saybur/hootswitch/firmware/control.c

/*
 * Copyright (C) 2024-2026 saybur
 *
 * This Source Code Form is subject to the terms of the Mozilla Public
 * License, v. 2.0. If a copy of the MPL was not distributed with this
 * file, You can obtain one at https://mozilla.org/MPL/2.0/.
 */

#include <stdio.h>
#include <hardware/watchdog.h>

#include <tusb.h>

#include <FreeRTOS.h>
#include <stream_buffer.h>
#include <task.h>

#include "computer.h"
#include "config.h"
#include "control.h"
#include "debug.h"

#include "drivers/serial.h"

#ifdef HOOTSWITCH_WIRELESS
#include "btscan.h"
#endif

#define WATCHDOG_SCRATCH_REG   0

#define CONTROL_WDRST_DEBUG    0xA5A5A5A5
#define CONTROL_BUFFER_SIZE    64

#define CONTROL_CHAR_END       0xC0
#define CONTROL_CHAR_ESC       0xDB
#define CONTROL_CHAR_ESC_END   0xDC
#define CONTROL_CHAR_ESC_ESC   0xDD

static void control_reboot(bool debug)
{
	// set flag to pause restarting, if needed
	if (debug) {
		watchdog_hw->scratch[WATCHDOG_SCRATCH_REG] = CONTROL_WDRST_DEBUG;
	}

	// perform watchdog reset
	watchdog_enable(1, 1);
	while(1);
}

control_reset_type control_check_reset(void)
{
	// retrieve and clear any special flags
	uint32_t w = watchdog_hw->scratch[WATCHDOG_SCRATCH_REG];
	watchdog_hw->scratch[WATCHDOG_SCRATCH_REG] = 0;

	// if the watchdog was responsible for the reset,
	// check if it was a special condition we need to report
	if (watchdog_enable_caused_reboot()) {
		switch (w) {
			case CONTROL_WDRST_DEBUG:
				return RESET_TYPE_DEBUG;
		}
	}

	// fallback to normal
	return RESET_TYPE_NORMAL;
}

/*
 * ----------------------------------------------------------------------------
 *   SLIP Decoding
 * ----------------------------------------------------------------------------
 *
 * This is stateful, ensure it only gets called from the control task.
 */

static uint8_t control_buffer[CONTROL_BUFFER_SIZE];
static uint8_t control_buffer_length;

static void control_enqueue(unsigned char c)
{
	if (control_buffer_length < CONTROL_BUFFER_SIZE) {
		control_buffer[control_buffer_length++] = c;
	} else {
		dbg_err("control overflow!");
	}
}

static void control_commit(void)
{
	/*
	 * Don't consider no-op ends to be an error, serial interface may do this
	 * to reset the session.
	 */
	if (control_buffer_length < 1) return;

	if (control_buffer[0] >= CONTROL_CODE_SEGMENT) {
		switch (control_buffer[0]) {
			case CONTROL_BT_SCAN:
#ifdef HOOTSWITCH_WIRELESS
				bt_scan();
#endif
				break;
			case CONTROL_DBG_TRACE:
				dbg_trace_enable(!dbg_trace_is_enabled());
				break;
			case CONTROL_DBG_HEAP:
				dbg_stats(DEBUG_RUNTIME_HEAP);
				break;
			case CONTROL_DBG_LIST:
				dbg_stats(DEBUG_RUNTIME_LIST);
				break;
			case CONTROL_DBG_STATS:
				dbg_stats(DEBUG_RUNTIME_STATS);
				break;
			case CONTROL_REBOOT:
				control_reboot(false);
				break;
			case CONTROL_REBOOT_DEBUG:
				control_reboot(true);
				break;
		}
	} else {
		serial_enqueue(control_buffer, control_buffer_length);
	}

	control_buffer_length = 0;
}

static void control_process(unsigned char c)
{
	static bool escaped = false;

	if (escaped) {
		escaped = false;
		switch (c) {
			case CONTROL_CHAR_END:
				// technically error, ignore to allow for reset
				control_commit();
				break;
			case CONTROL_CHAR_ESC_END:
				control_enqueue(CONTROL_CHAR_END);
				break;
			case CONTROL_CHAR_ESC_ESC:
				control_enqueue(CONTROL_CHAR_ESC);
				break;
			default:
				dbg_err("control bad esc %02X", c);
		}
	} else {
		switch (c) {
			case CONTROL_CHAR_END:
				control_commit();
				break;
			case CONTROL_CHAR_ESC:
				escaped = true;
				break;
			default:
				control_enqueue(c);
		}
	}
}

/*
 * ----------------------------------------------------------------------------
 *   Data Handoff Logic
 * ----------------------------------------------------------------------------
 *
 * This uses a FreeRTOS stream buffer to pass from producer (TinyUSB) to
 * consumer (control task).
 */

static volatile StreamBufferHandle_t stream = NULL;

void tud_cdc_rx_cb(uint8_t itf)
{
	if (!stream) return;

	uint8_t data[CONTROL_BUFFER_SIZE];
	uint32_t data_read = tud_cdc_read(data, sizeof(data));
	if (data_read > 0) {
		uint32_t data_write = xStreamBufferSend(stream, data, data_read, 0);
		if (data_write != data_read) {
			dbg("cdc read dropped %d bytes", data_read - data_write);
		}
	}
}

void control_task(__unused void *parameters)
{
	// create stream for 2x max read size above is, triggering on 1 byte
	stream = xStreamBufferCreate(CONTROL_BUFFER_SIZE * 2, 0);

	unsigned char data[CONTROL_BUFFER_SIZE];
	while (true) {
		uint16_t data_read = xStreamBufferReceive(
				stream, data, CONTROL_BUFFER_SIZE, portMAX_DELAY);
		for (uint16_t i = 0; i < data_read; i++) {
			control_process(data[i]);
		}
	}
}
