saybur/hootswitch/firmware/driver.c

/*
 * Copyright (C) 2024-2026 saybur
 *
 * This Source Code Form is subject to the terms of the Mozilla Public
 * License, v. 2.0. If a copy of the MPL was not distributed with this
 * file, You can obtain one at https://mozilla.org/MPL/2.0/.
 */

#include "pico/stdlib.h"

#include "computer.h"
#include "driver.h"
#include "hardware.h"

#include "drivers/virtual.h"

static dev_driver *device_list[DEVICE_MAX];
static uint32_t references[DEVICE_MAX];
static uint8_t device_list_count;

uint8_t driver_count_devices(void)
{
	return device_list_count;
}

bool driver_register(uint8_t *index, dev_driver *driver, uint32_t ref)
{
	if (driver == NULL) {
		return false;
	}

	if (device_list_count < DEVICE_MAX) {
		if (index != NULL) {
			*index = device_list_count;
		}
		device_list[device_list_count] = driver;
		references[device_list_count] = ref;
		device_list_count++;
		return true;
	} else {
		return false;
	}
}

bool driver_get(uint8_t index, dev_driver **driver, uint32_t *ref)
{
	if (index < device_list_count) {
		*driver = device_list[index];
		if (ref != NULL) {
			*ref = references[index];
		}
		return true;
	} else {
		return false;
	}
}

void driver_init(void)
{
	/*
	 * ------------------------------------------------------------------------
	 * This space available for drivers to tie into the system. Call init code
	 * from here to set up during boot.
	 * ------------------------------------------------------------------------
	 */

	virtual_init();
}
