saybur/hootswitch/firmware/host.h

/*
 * Copyright (C) 2024-2026 saybur
 *
 * This Source Code Form is subject to the terms of the Mozilla Public
 * License, v. 2.0. If a copy of the MPL was not distributed with this
 * file, You can obtain one at https://mozilla.org/MPL/2.0/.
 */

#ifndef __HOST_H__
#define __HOST_H__

#include "handler.h"
#include "host_err.h"

typedef enum {
	COMMAND_FLUSH =    0x1,
	COMMAND_LISTEN_0 = 0x8,
	COMMAND_LISTEN_1 = 0x9,
	COMMAND_LISTEN_2 = 0xA,
	COMMAND_LISTEN_3 = 0xB,
	COMMAND_TALK_0 =   0xC,
	COMMAND_TALK_1 =   0xD,
	COMMAND_TALK_2 =   0xE,
	COMMAND_TALK_3 =   0xF
} bus_command;

/**
 * Executes an asynchronous command on the host bus.
 *
 * This copies the command into a queue and returns. The registered handler
 * callback will be invoked once the host controller has a chance to get to
 * your request.
 *
 * This is not needed for some devices: the controller will auto-poll Register
 * 0 on any device that issues a SRQ, so if you are the handler for a device
 * you'll still get calls whenever the native device issues a SRQ and returns
 * data for Talk 0. These calls will have an ID of 0.
 *
 * @param dev   device number from the register call.
 * @param cmd   ADB command to execute (suggest using bus_command above).
 * @param id    will be assigned an identifier, which will match the callback;
 *              may be NULL, which uses a default ID callback of 0.
 * @param data  up to 8 bytes of data if a Listen command, ignored otherwise.
 * @param len   length of data if Listen, ignored otherwise.
 * @return      true if the request could be queued, false otherwise; this is
 *              due to the queue being full or an invalid device.
 */
host_err host_cmd(uint8_t dev, uint8_t cmd, uint32_t *id,
		uint8_t *data, uint8_t len);

/**
 * Registers a handler with the host. Only handlers registered during reset
 * will have devices assigned to them (if any are on the bus).
 *
 * @param *handler  pointer to a handler, which will be copied locally.
 * @return          any errors.
 */
host_err host_register(ndev_handler *handler);

/**
 * Executes a bus reset command on the host side. This should only be done
 * during initial device startup.
 *
 * This will disable async commands and force a reset. Devices may take some
 * time to come out of reset and begin accepting commands again. This will
 * return once the command completes. Wait an appropriate time before calling
 * host_reset_devices() to finish the reset process.
 *
 * @return      any errors.
 */
host_err host_reset_bus(void);

/**
 * Reconfigures all devices following a bus reset command on the host side.
 * This should only be done during initial device startup.
 *
 * This will perform the "address shuffle" required by ADB following a reset.
 * You must call the above command prior to calling this one, with an
 * appropriate delay included to avoid devices still being stuck in reset when
 * this begins execution.
 *
 * @return      any errors.
 */
host_err host_reset_devices(void);

/**
 * Performs the post-reset address resolution step, sets up the host device
 * table, and assigns the handlers to their various devices.
 *
 * Because of the randomness in ADB addresses there are no guarantees that a
 * particular handler will get a particular device if there is competition.
 *
 * This runs exclusively in polling mode and will hog the CPU. While I've tried
 * to make it safe to execute post-boot, this should generally only be called
 * during startup.
 *
 * @return      any errors.
 */
host_err host_readdress(void);

/**
 * Initializes hardware to use with the host. Users should not call this
 * function.
 */
void host_init(void);

// TEMPORARY
void host_poll(void);

/**
 * Task responsible for processing data responses to the handlers. Users should
 * not call this function.
 */
void host_task(void *parameters);

#endif /* __HOST_H__ */
