saybur/hootswitch/firmware/device.h

/*
 * Copyright (C) 2024 saybur
 *
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
 * You should have received a copy of the GNU General Public License
 * along with this program.  If not, see <https://www.gnu.org/licenses/>.
 */

#ifndef __DEVICE_H__
#define __DEVICE_H__

void device_init(void);

#endif /* __DEVICE_H__ */
